MathematicalPotato/MP_DooKi3_SLM_Designs/MP_DooKi3_XY_Stuff/XY_Idlers/STLs/MP_DooKi3_SLM_XY_V6_XDrive_BottomFront_x1.stl

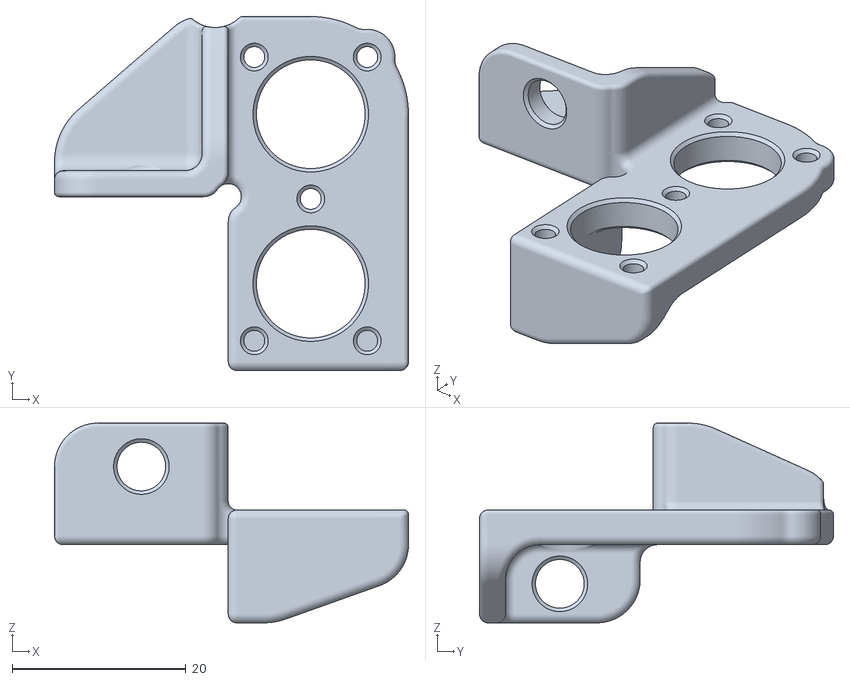
[picture p25: CAD file, 2024-08-21]
MP_DooKi3_XY_Stuff/XY_Idlers/STLs/MP_DooKi3_SLM_XY_V6_XDrive_BottomFront_x1.stl
40.8 x 40.8 x 23.0
