MathematicalPotato/MP_DooKi3_SLM_Designs/MP_DooKi3_Z_Stuff/Z_Maxwell_Mounts/CAD/MP_DooKi3_SLM_Z_Maxwell_ClampPlate_V3_x3.dxf

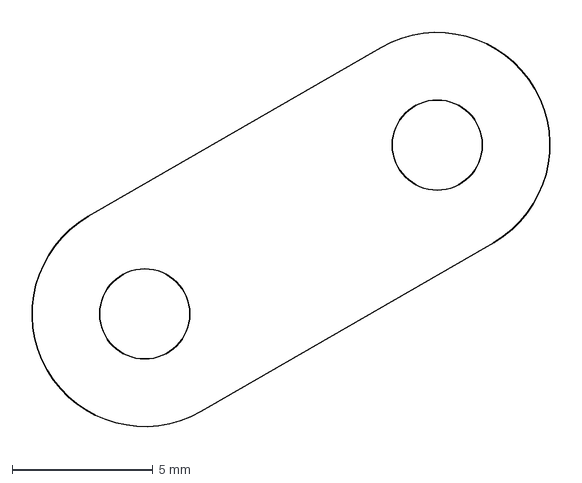
[picture p26: CAD file, 2024-08-07]
MP_DooKi3_Z_Stuff/Z_Maxwell_Mounts/CAD/MP_DooKi3_SLM_Z_Maxwell_ClampPlate_V3_x3.dxf
19.5 x 15.1 mm
