MathematicalPotato/MP_DooKi3_SLM_Designs/MP_DooKi3_XY_Stuff/XY_Idlers/STLs/MP_DooKi3_SLM_XY_V6_YDrive_Bottom_x2.stl

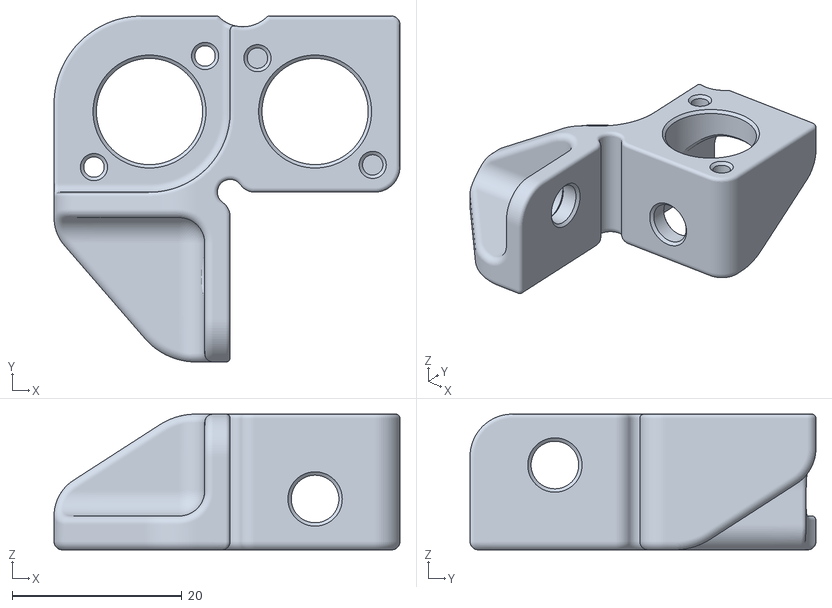
[picture p27: CAD file, 2024-08-21]
MP_DooKi3_XY_Stuff/XY_Idlers/STLs/MP_DooKi3_SLM_XY_V6_YDrive_Bottom_x2.stl
40.8 x 40.8 x 16.0
