MathematicalPotato/MP_DooKi3_SLM_Designs/MP_DooKi3_Z_Stuff/Z_Maxwell_Mounts/STLs/MP_DooKi3_SLM_Z_Maxwell_Clamp_V4_x3.stl

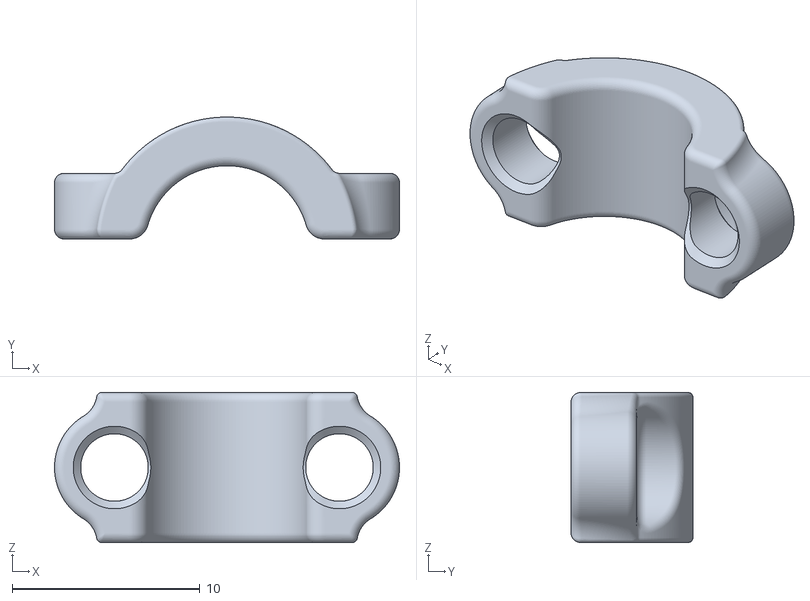
[picture p28: CAD file, 2024-09-10]
MP_DooKi3_Z_Stuff/Z_Maxwell_Mounts/STLs/MP_DooKi3_SLM_Z_Maxwell_Clamp_V4_x3.stl
18.4 x 6.50 x 8.00
