MathematicalPotato/MP_DooKi3_SLM_Designs/MP_DooKi3_XY_Stuff/XY_Tensioners/STLs/MP_DooKi3_SLM_Y_Spacer_21mm_V2_x2.stl

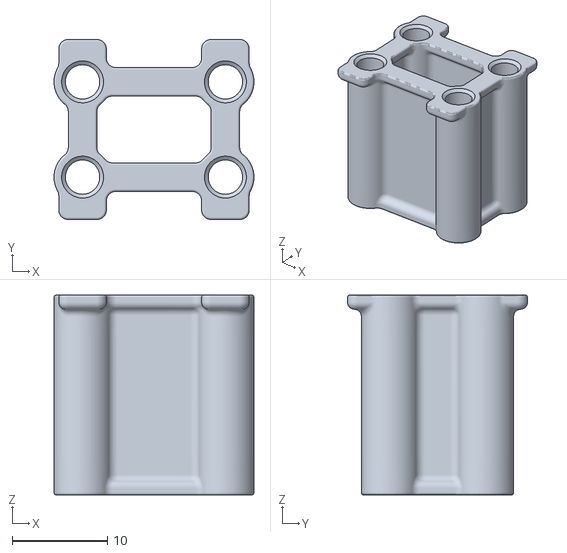
[picture p30: CAD file, 2025-02-20]
MP_DooKi3_XY_Stuff/XY_Tensioners/STLs/MP_DooKi3_SLM_Y_Spacer_21mm_V2_x2.stl
21.0 x 18.9 x 21.0
