MathematicalPotato/MP_DooKi3_SLM_Designs/MP_DooKi3_XY_Stuff/XY_Tensioners/STLs/MP_DooKi3_SLM_XY_6.0mm_Rail_Mount_V3_Mirror_x2.stl

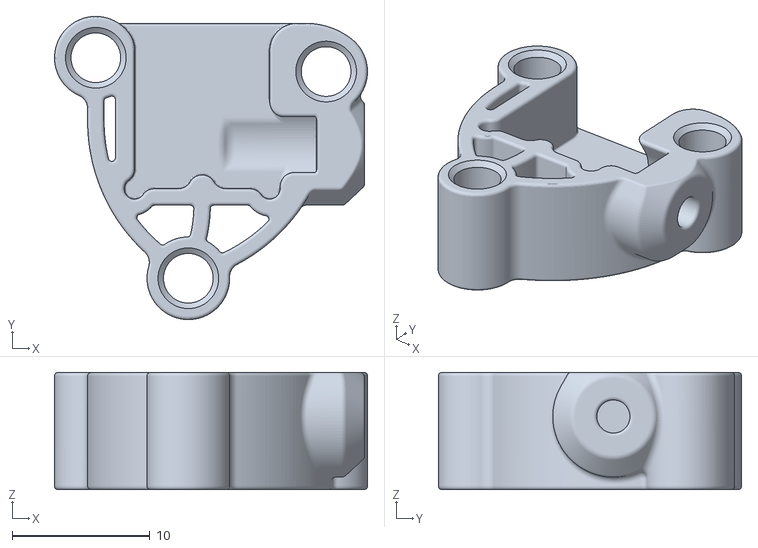
[picture p32: CAD file, 2025-02-20]
MP_DooKi3_XY_Stuff/XY_Tensioners/STLs/MP_DooKi3_SLM_XY_6.0mm_Rail_Mount_V3_Mirror_x2.stl
22.7 x 22.0 x 8.50
