MathematicalPotato/MP_DooKi3_SLM_Designs/MP_DooKi3_XY_Stuff/XY_Tensioners/STLs/MP_DooKi3_SLM_XY_6.5mm_Rail_Mount_V3_x2.stl

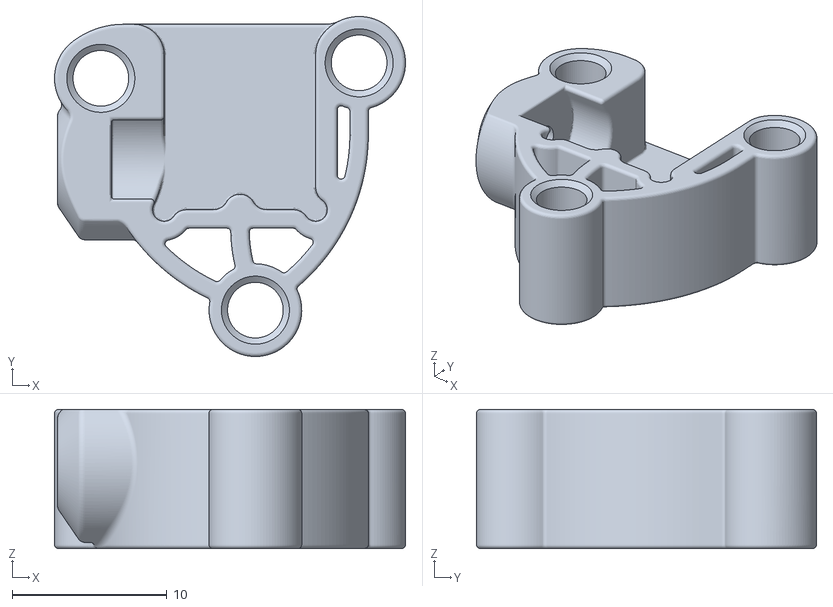
[picture p33: CAD file, 2024-09-07]
MP_DooKi3_XY_Stuff/XY_Tensioners/STLs/MP_DooKi3_SLM_XY_6.5mm_Rail_Mount_V3_x2.stl
22.7 x 22.0 x 9.00
