MathematicalPotato/MP_DooKi3_SLM_Designs/MP_DooKi3_XY_Stuff/XY_Tensioners/STLs/MP_DooKi3_SLM_Y_Spacer_20mm_V2_x2.stl

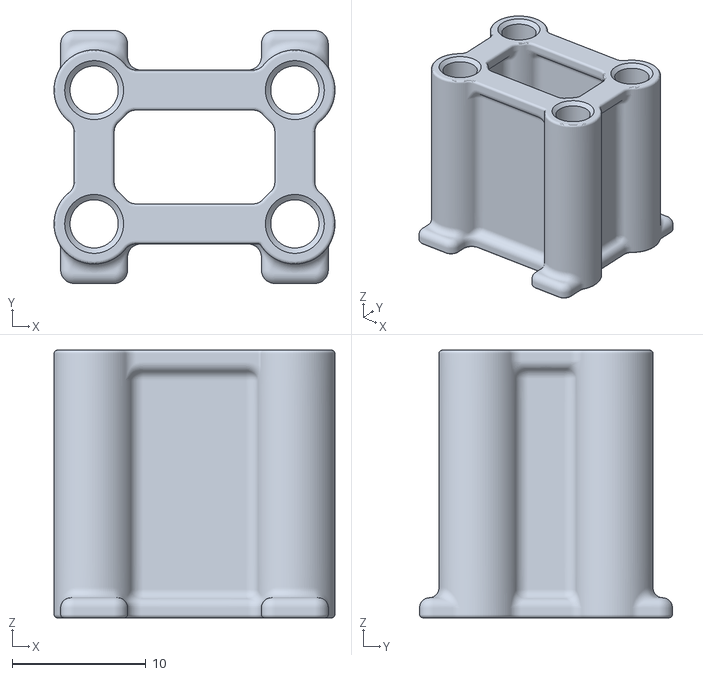
[picture p34: CAD file, 2024-08-21]
MP_DooKi3_XY_Stuff/XY_Tensioners/STLs/MP_DooKi3_SLM_Y_Spacer_20mm_V2_x2.stl
21.0 x 18.9 x 20.0
